MarianAldenhoevel/Mamelet/Marquee.jpg

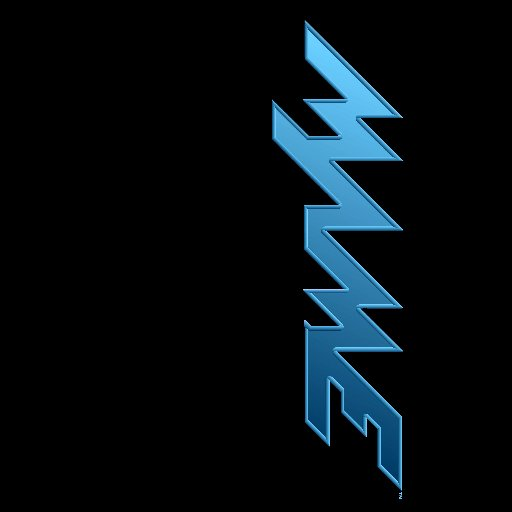
Marquee.jpg
